hggh/7seg-clock/include/numbers.h

const static uint8_t numbers[10][14] = {
  // 0
  {1, 1, 1, 1, 1, 1, 1, 1, 0, 0, 1, 1, 1, 1},
  // 1
  {0, 0, 0, 0, 0, 0, 1, 1, 0, 0, 1, 1, 0, 0},
  // 2
  {1, 1, 0, 0, 1, 1, 1, 1, 1, 1, 0, 0, 1, 1},
  // 3
  {0, 0, 0, 0, 1, 1, 1, 1, 1, 1, 1, 1, 1, 1},
  // 4
  {0, 0, 1, 1, 0, 0, 1, 1, 1, 1, 1, 1, 0, 0},
  // 5
  {0, 0, 1, 1, 1, 1, 0, 0, 1, 1, 1, 1, 1, 1},
  // 6
  {1, 1, 1, 1, 1, 1, 0, 0, 1, 1, 1, 1, 1, 1},
  // 7
  {0 ,0, 0, 0, 1, 1, 1, 1, 1, 1, 1, 1, 0, 0},
  // 8
  {1, 1, 1, 1, 1, 1, 1, 1, 1, 1, 1, 1, 1, 1},
  // 9
  {0, 0, 1, 1, 1, 1, 1, 1, 1, 1, 1, 1, 1, 1},
};
